IvanHvezda/LED-CUBE-8x8x8/Aplikace/část programu aplikace 2.png

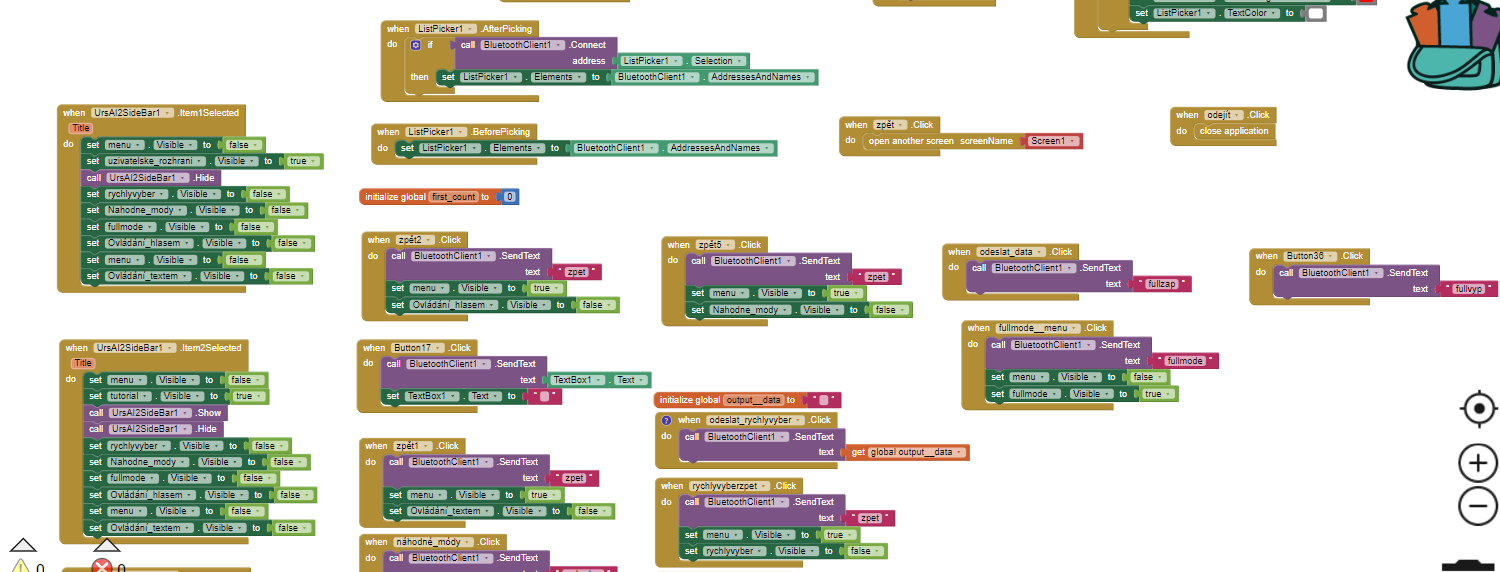
Aplikace/část programu aplikace 2.png
