IvanHvezda/LED-CUBE-8x8x8/Aplikace/část programu aplikace 3.png

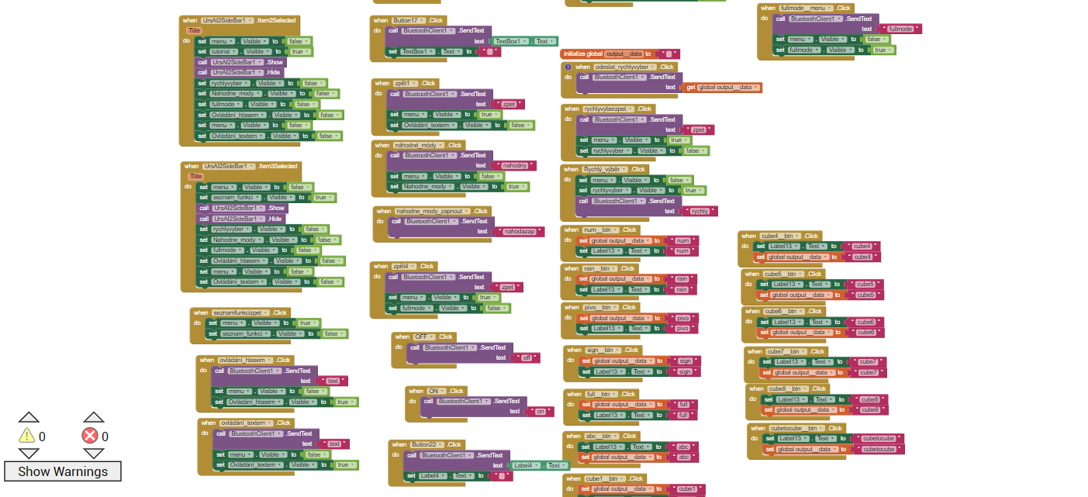
Aplikace/část programu aplikace 3.png
