IvanHvezda/LED-CUBE-8x8x8/Aplikace/část programu aplikace 4.png

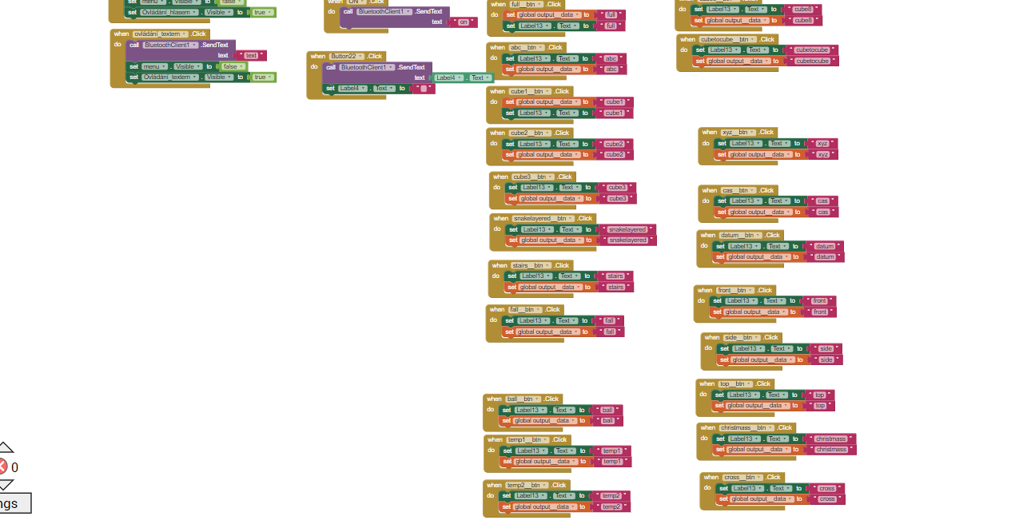
Aplikace/část programu aplikace 4.png
