IvanHvezda/LED-CUBE-8x8x8/Elektrická část/512 LED.jpg

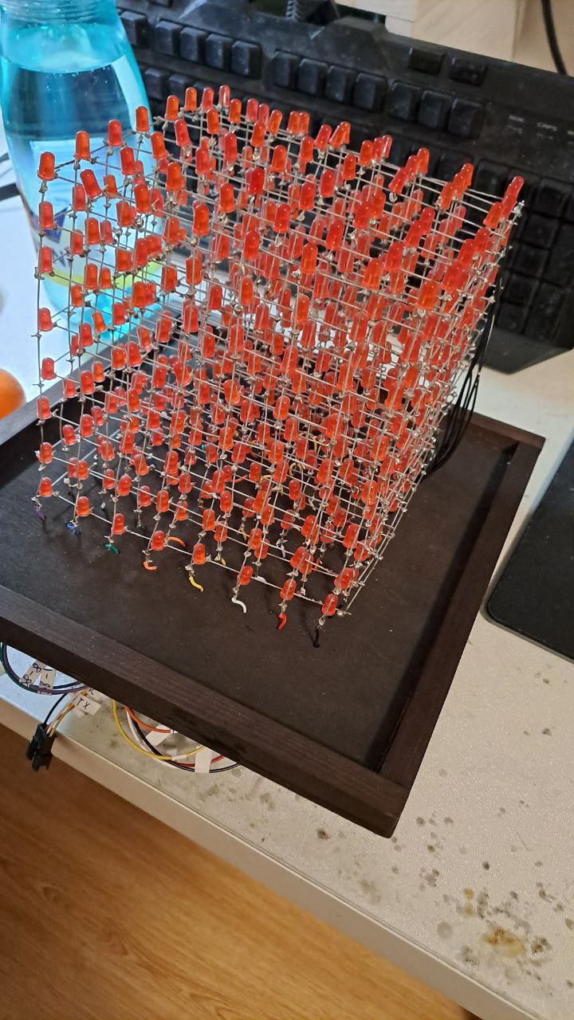
Elektrická část/512 LED.jpg
