IvanHvezda/LED-CUBE-8x8x8/Elektrická část/blokové schéma.png

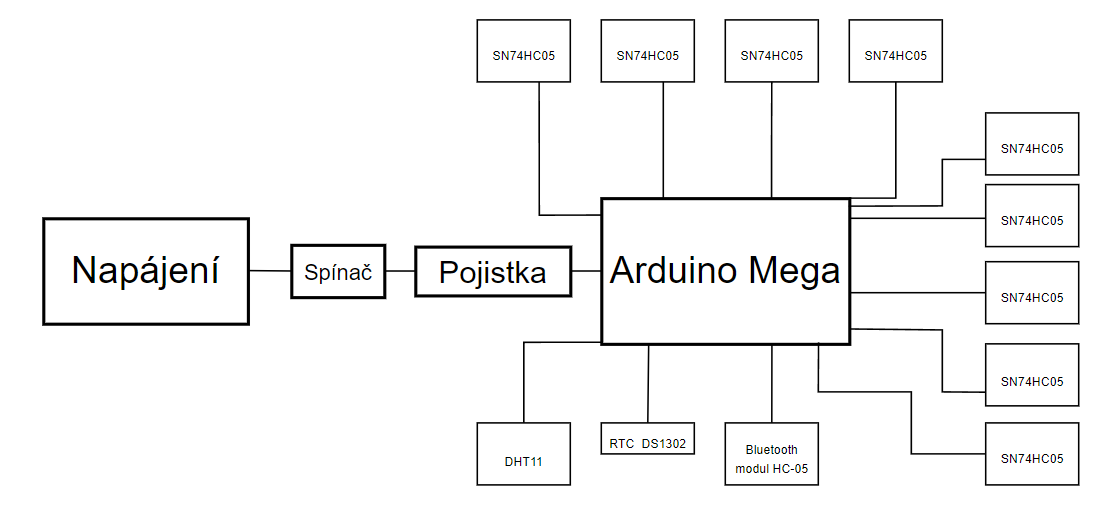
Elektrická část/blokové schéma.png
