IvanHvezda/LED-CUBE-8x8x8/Elektrická část/DPS včetně LED.jpg

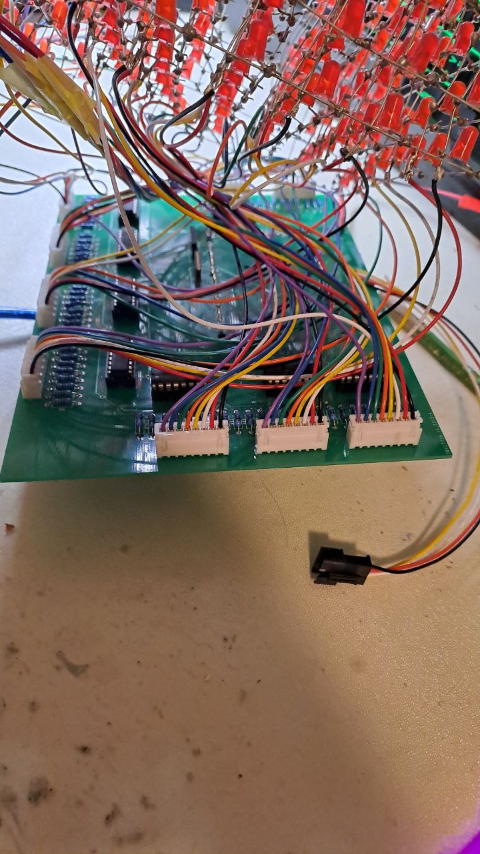
Elektrická část/DPS včetně LED.jpg
