IvanHvezda/LED-CUBE-8x8x8/Elektrická část/Popis vodičů 2.jpg

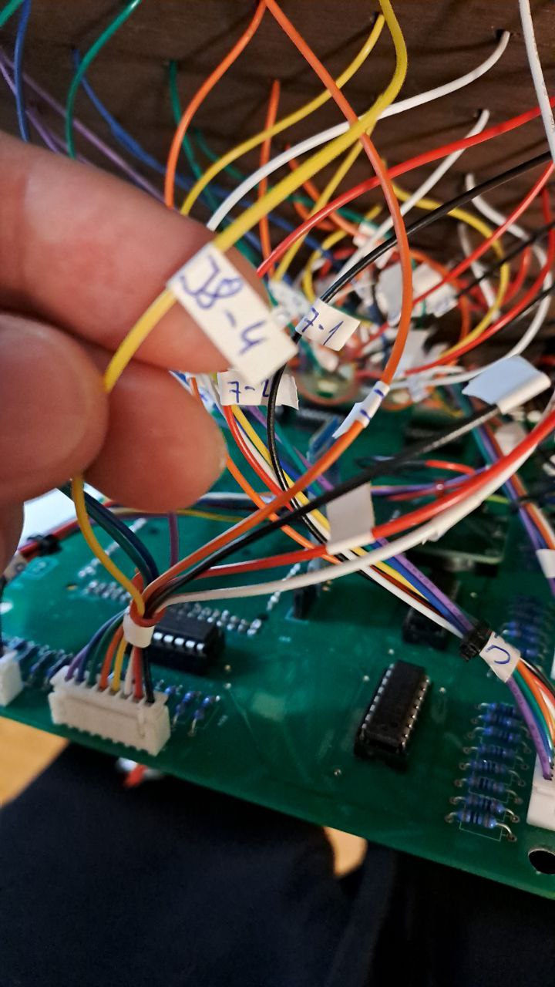
Elektrická část/Popis vodičů 2.jpg
