IvanHvezda/LED-CUBE-8x8x8/Elektrická část/Pouze elektro.jpg

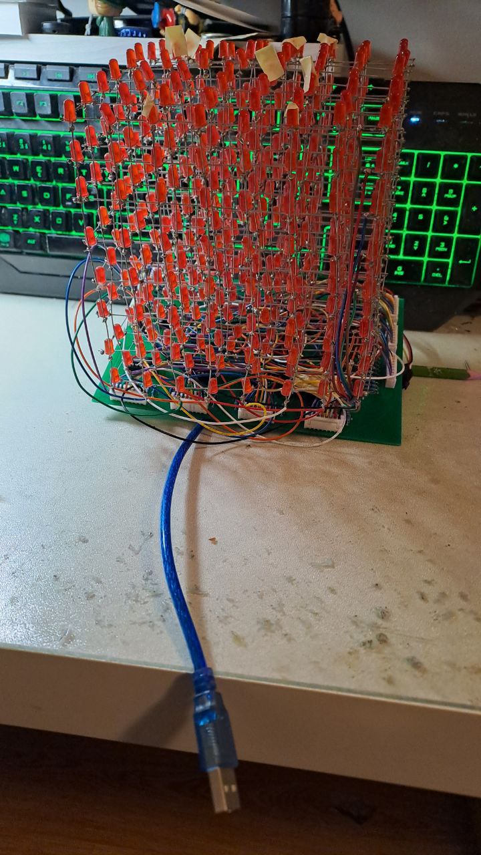
Elektrická část/Pouze elektro.jpg
