IvanHvezda/LED-CUBE-8x8x8/Konstrukce/Celá kosntrukce 2.jpg

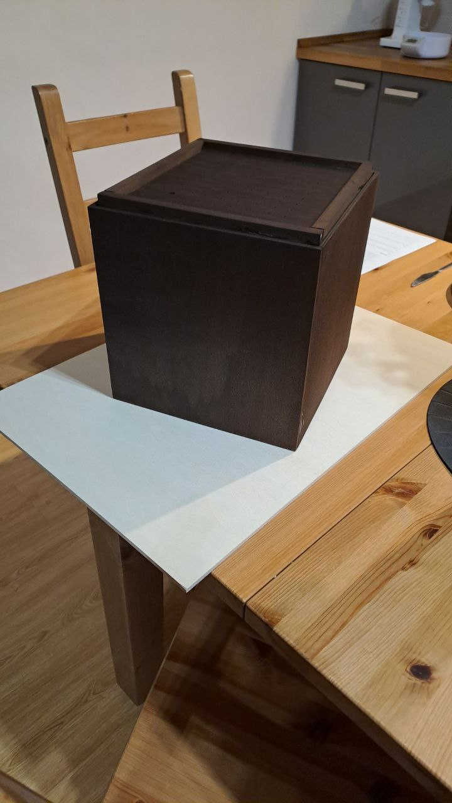
Konstrukce/Celá kosntrukce 2.jpg
