IvanHvezda/LED-CUBE-8x8x8/Konstrukce/Začátek stavby konstrukce.jpg

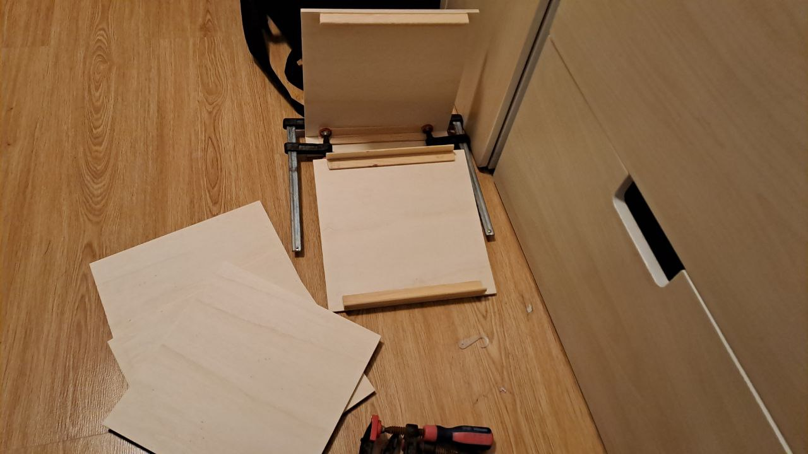
Konstrukce/Začátek stavby konstrukce.jpg
