IvanHvezda/LED-CUBE-8x8x8/Konstrukce/Čerstvě natřená konstrukce 1.jpg

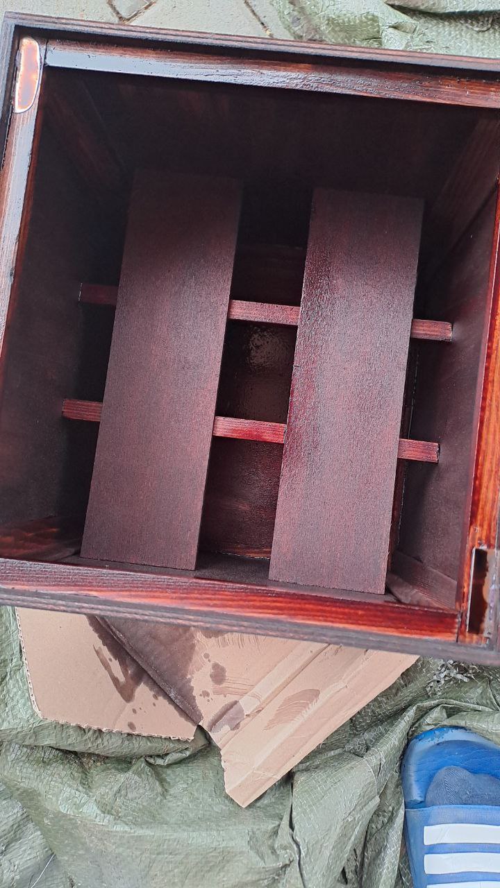
Konstrukce/Čerstvě natřená konstrukce 1.jpg
