IvanHvezda/LED-CUBE-8x8x8/Média/média 1.jpg

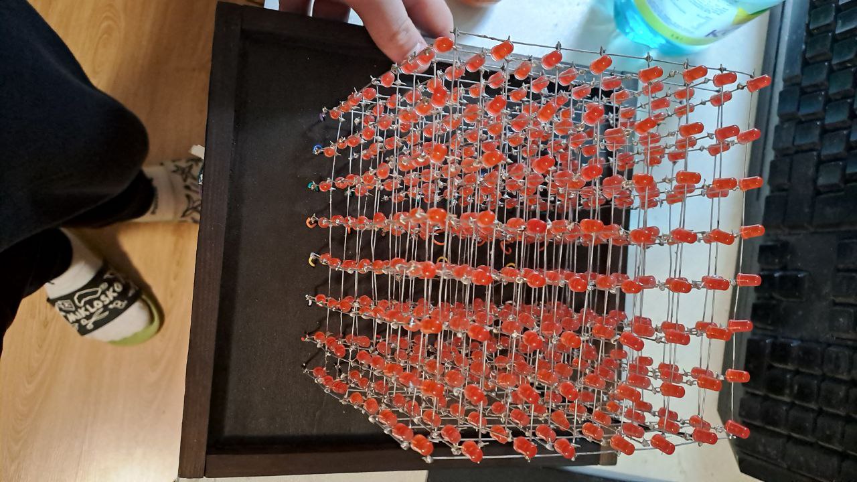
Média/média 1.jpg
