IvanHvezda/LED-CUBE-8x8x8/Média/média 2.jpg

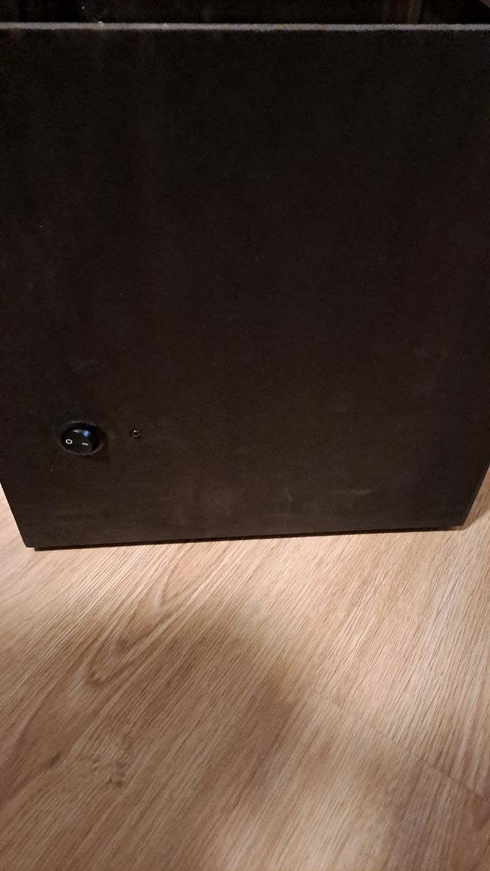
Média/média 2.jpg
