IvanHvezda/LED-CUBE-8x8x8/Média/média 4.jpg

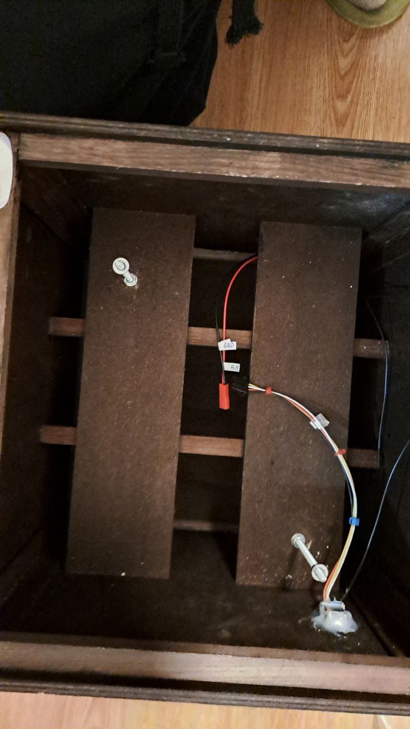
Média/média 4.jpg
