IvanHvezda/LED-CUBE-8x8x8/Média/média 5.jpg

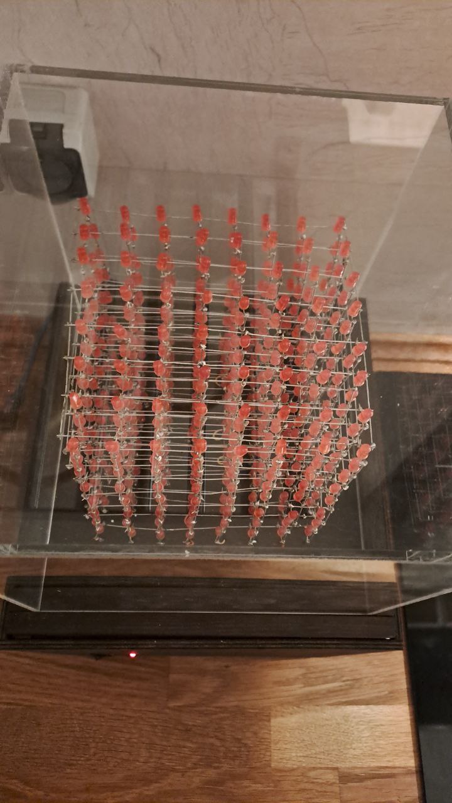
Média/média 5.jpg
