IvanHvezda/LED-CUBE-8x8x8/Média/média 6.jpg

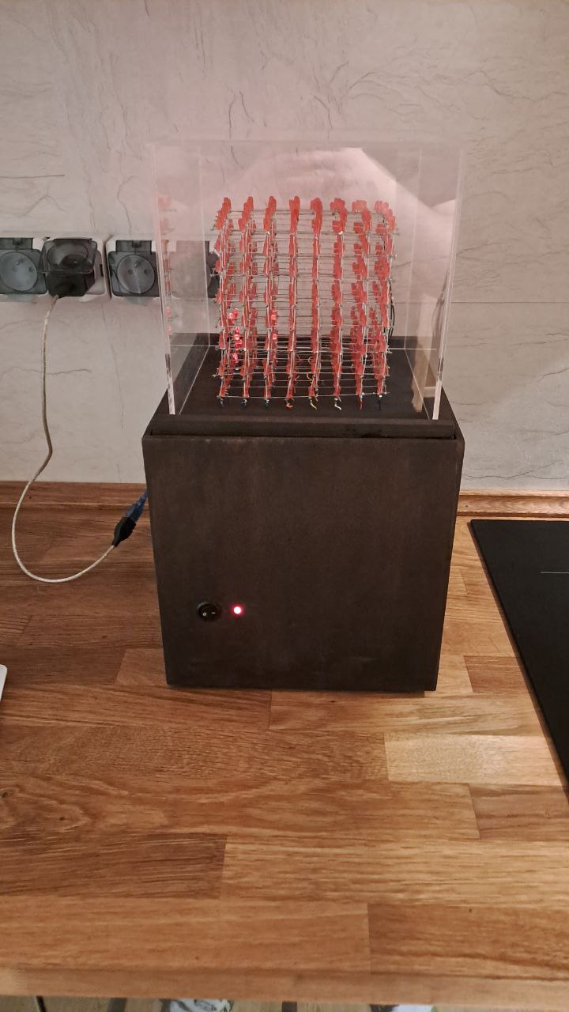
Média/média 6.jpg
