IvanHvezda/LED-CUBE-8x8x8/Média/média 7.jpg

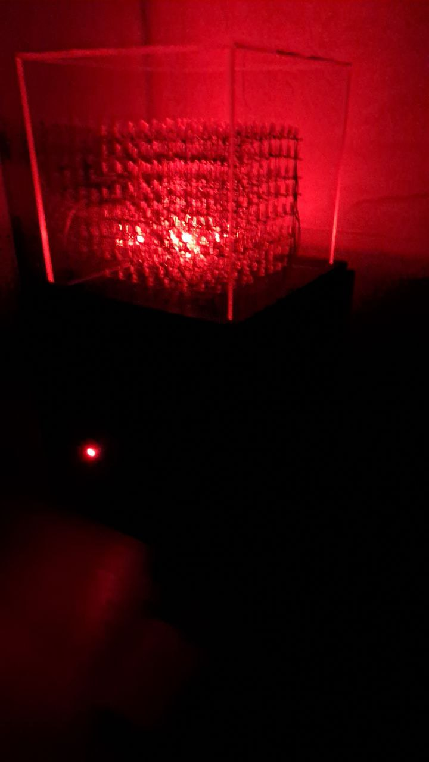
Média/média 7.jpg
