IvanHvezda/LED-CUBE-8x8x8/Média/média 8.jpg

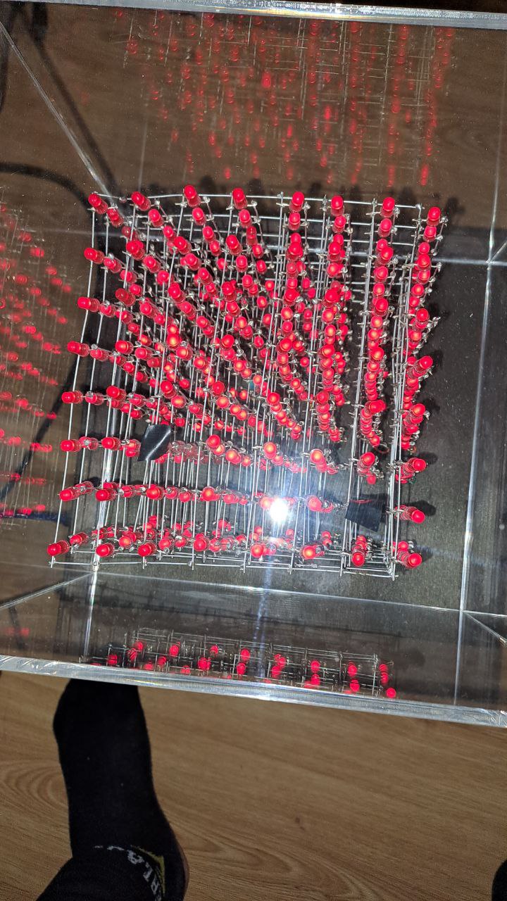
Média/média 8.jpg
