IvanHvezda/LED-CUBE-8x8x8/Média/média 9.jpg

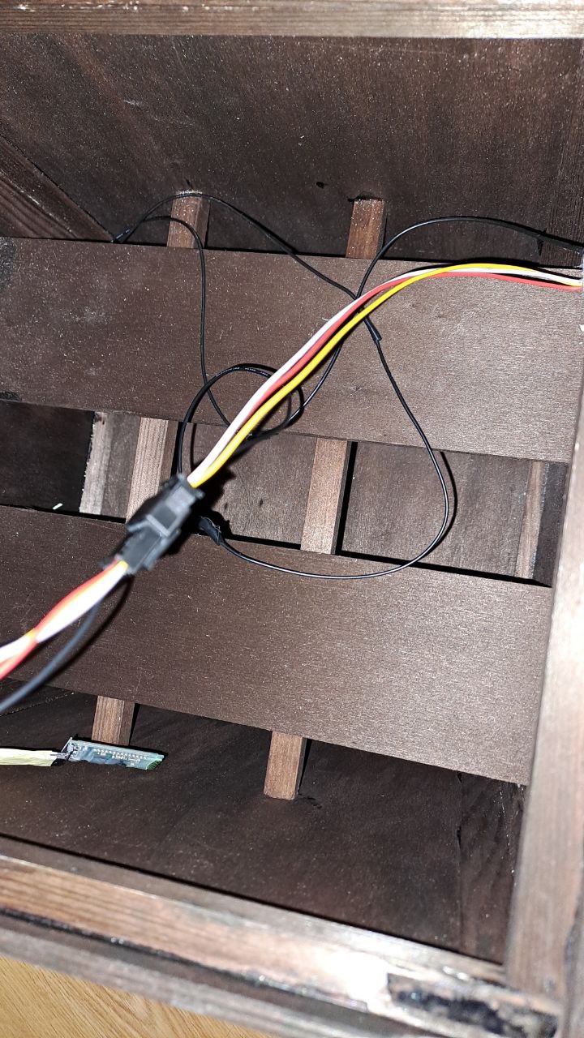
Média/média 9.jpg
