IvanHvezda/LED-CUBE-8x8x8/Média/média 11.jpg

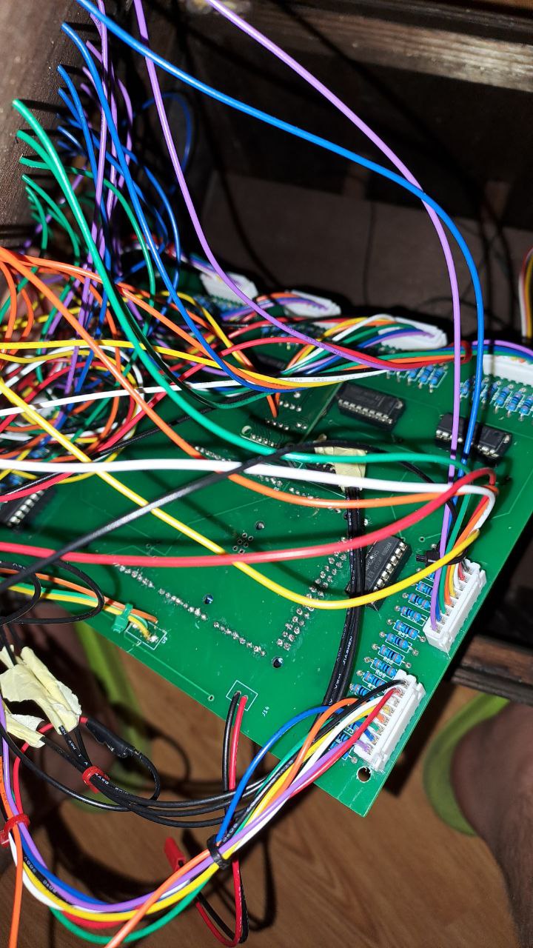
Média/média 11.jpg
