IvanHvezda/LED-CUBE-8x8x8/Média/média 12.jpg

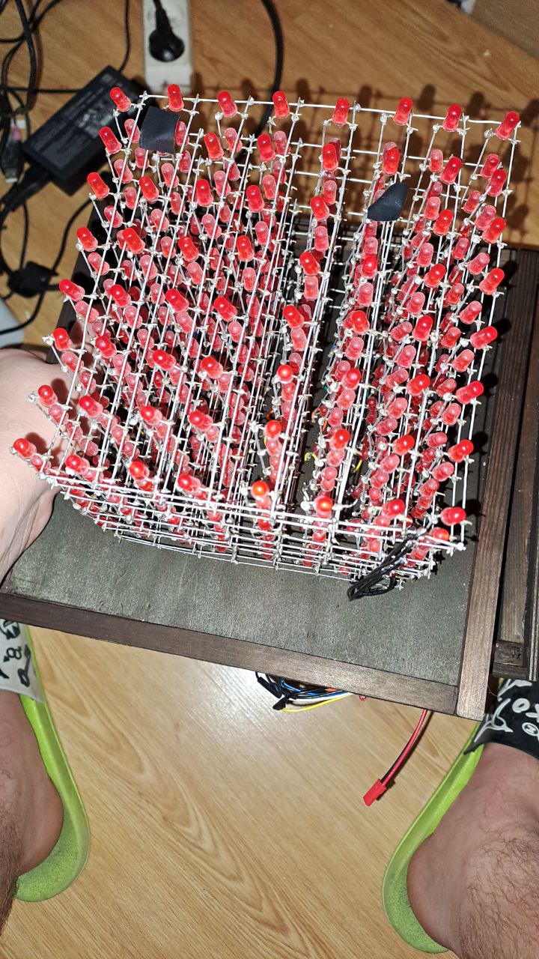
Média/média 12.jpg
