IvanHvezda/LED-CUBE-8x8x8/Média/média 14.jpg

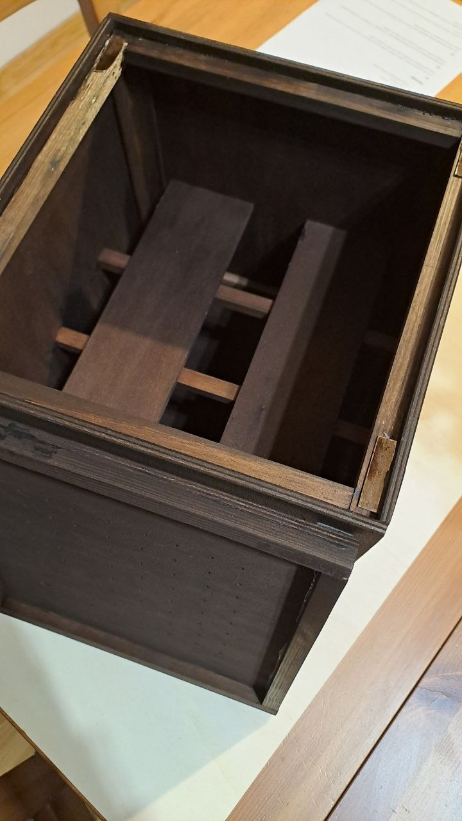
Média/média 14.jpg
