IvanHvezda/LED-CUBE-8x8x8/Média/média 15.jpg

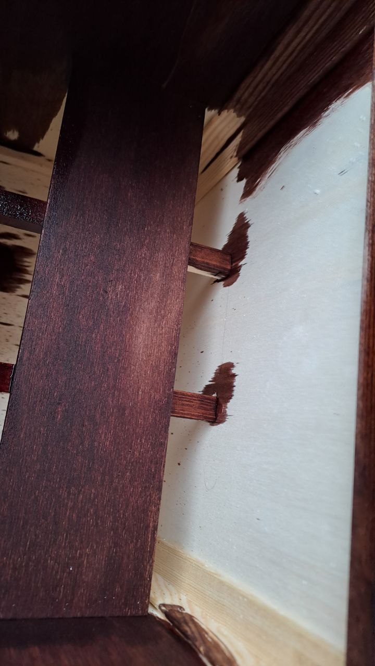
Média/média 15.jpg
