IvanHvezda/LED-CUBE-8x8x8/Média/média 17.jpg

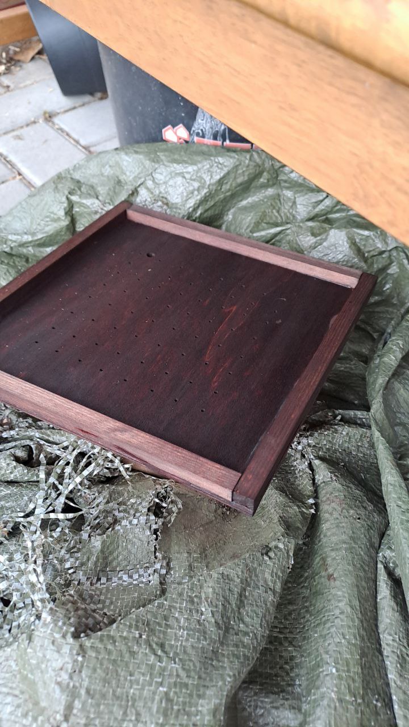
Média/média 17.jpg
