IvanHvezda/LED-CUBE-8x8x8/Média/média 18.jpg

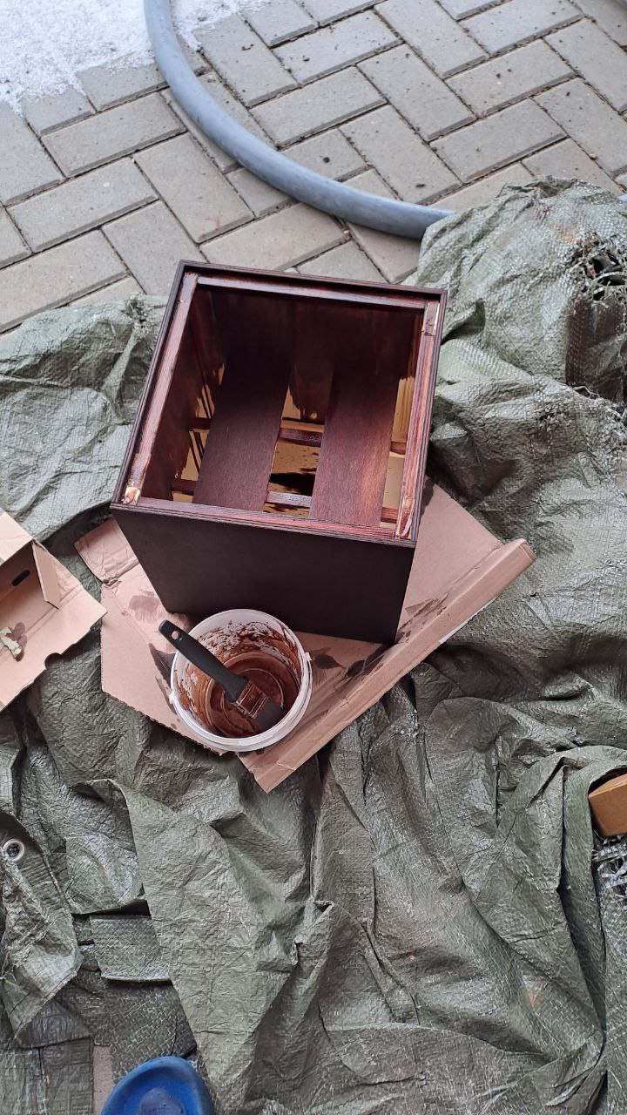
Média/média 18.jpg
