IvanHvezda/LED-CUBE-8x8x8/Média/média 19.jpg

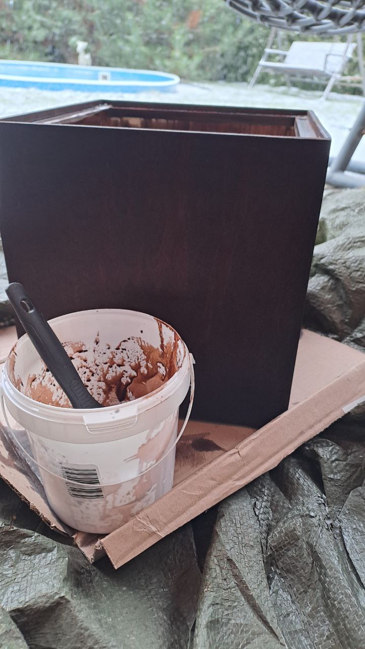
Média/média 19.jpg
