IvanHvezda/LED-CUBE-8x8x8/Média/média 20.jpg

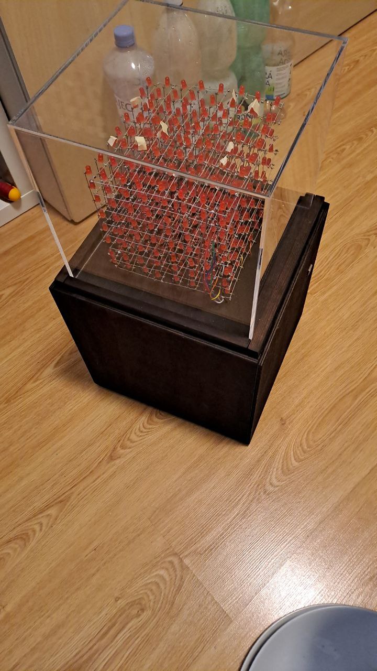
Média/média 20.jpg
