IvanHvezda/LED-CUBE-8x8x8/Média/Odevzdání projektu 1.jpg

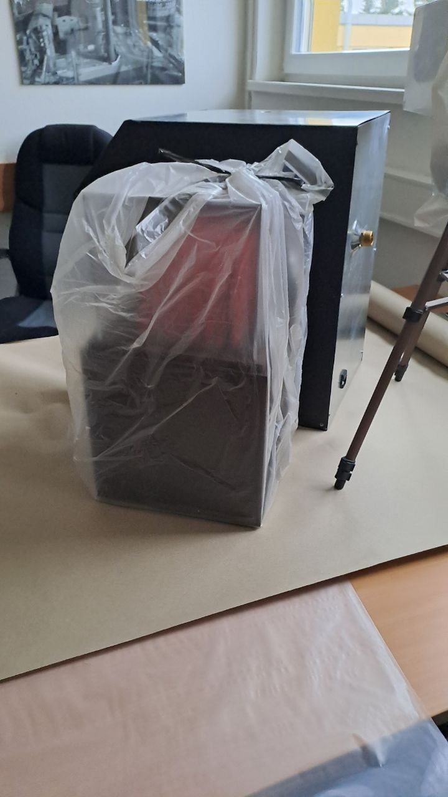
Média/Odevzdání projektu 1.jpg
