IvanHvezda/LED-CUBE-8x8x8/Program/Část kódu funkce abc.h.png

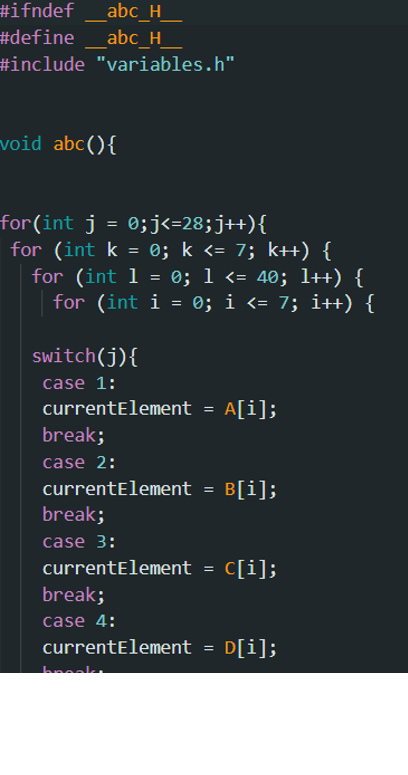
Program/Část kódu funkce abc.h.png
