IvanHvezda/LED-CUBE-8x8x8/Program/hvezdiv20kod/side.h

#ifndef __side_H__
#define __side_H__
#include "variables.h"



 void side(){
            int cas1 = 150;
 
     Serial.println(cas);
    digitalWrite(layers[0],0);
    digitalWrite(layers[1],0);
    digitalWrite(layers[2],0); 
    digitalWrite(layers[3],0);
    digitalWrite(layers[4],0);
    digitalWrite(layers[5],0);
    digitalWrite(layers[6],0);
    digitalWrite(layers[7],0);

    myByte = B11111111;
    leds__none = B00000000;

    digitalWrite(latchPin3,0);
    shiftOut(dataPin3,clockPin3,LSBFIRST,leds__none);
    digitalWrite(latchPin3,1);

    digitalWrite(latchPin1,0);
    shiftOut(dataPin1,clockPin1,LSBFIRST,myByte);
    digitalWrite(latchPin1,1);

    delay(cas1);

    digitalWrite(latchPin1,0);
    shiftOut(dataPin1,clockPin1,LSBFIRST,leds__none);
    digitalWrite(latchPin1,1);

    digitalWrite(latchPin2,0);
    shiftOut(dataPin2,clockPin2,LSBFIRST,myByte);
    digitalWrite(latchPin2,1);

      delay(cas1);

    digitalWrite(latchPin2,0);
    shiftOut(dataPin2,clockPin2,LSBFIRST,leds__none);
    digitalWrite(latchPin2,1);

    digitalWrite(latchPin3,0);
    shiftOut(dataPin3,clockPin3,LSBFIRST,myByte);
    digitalWrite(latchPin3,1);

      delay(cas1);

    digitalWrite(latchPin3,0);
    shiftOut(dataPin3,clockPin3,LSBFIRST,leds__none);
    digitalWrite(latchPin3,1);

    digitalWrite(latchPin4,0);
    shiftOut(dataPin4,clockPin4,LSBFIRST,myByte);
    digitalWrite(latchPin4,1);

      delay(cas1);

    digitalWrite(latchPin4,0);
    shiftOut(dataPin4,clockPin4,LSBFIRST,leds__none);
    digitalWrite(latchPin4,1);

    digitalWrite(latchPin5,0);
    shiftOut(dataPin5,clockPin5,LSBFIRST,myByte);
    digitalWrite(latchPin5,1);

        delay(cas1);

    digitalWrite(latchPin5,0);
    shiftOut(dataPin5,clockPin5,LSBFIRST,leds__none);
    digitalWrite(latchPin5,1);

    digitalWrite(latchPin6,0);
    shiftOut(dataPin6,clockPin6,LSBFIRST,myByte);
    digitalWrite(latchPin6,1);

        delay(cas1);

    digitalWrite(latchPin6,0);
    shiftOut(dataPin6,clockPin6,LSBFIRST,leds__none);
    digitalWrite(latchPin6,1);

    digitalWrite(latchPin7,0);
    shiftOut(dataPin7,clockPin7,LSBFIRST,myByte);
    digitalWrite(latchPin7,1);

        delay(cas1);

    digitalWrite(latchPin7,0);
    shiftOut(dataPin7,clockPin7,LSBFIRST,leds__none);
    digitalWrite(latchPin7,1);

    digitalWrite(latchPin8,0);
    shiftOut(dataPin8,clockPin8,LSBFIRST,myByte);
    digitalWrite(latchPin8,1);

      delay(cas1);

    digitalWrite(latchPin8,0);  
    shiftOut(dataPin8,clockPin8,LSBFIRST,leds__none);
    digitalWrite(latchPin8,1);

      cas1 = cas1 - 50;
    
    }

#endif
